jcoop1219/BME590L/Software/Software Flowchart.pdf

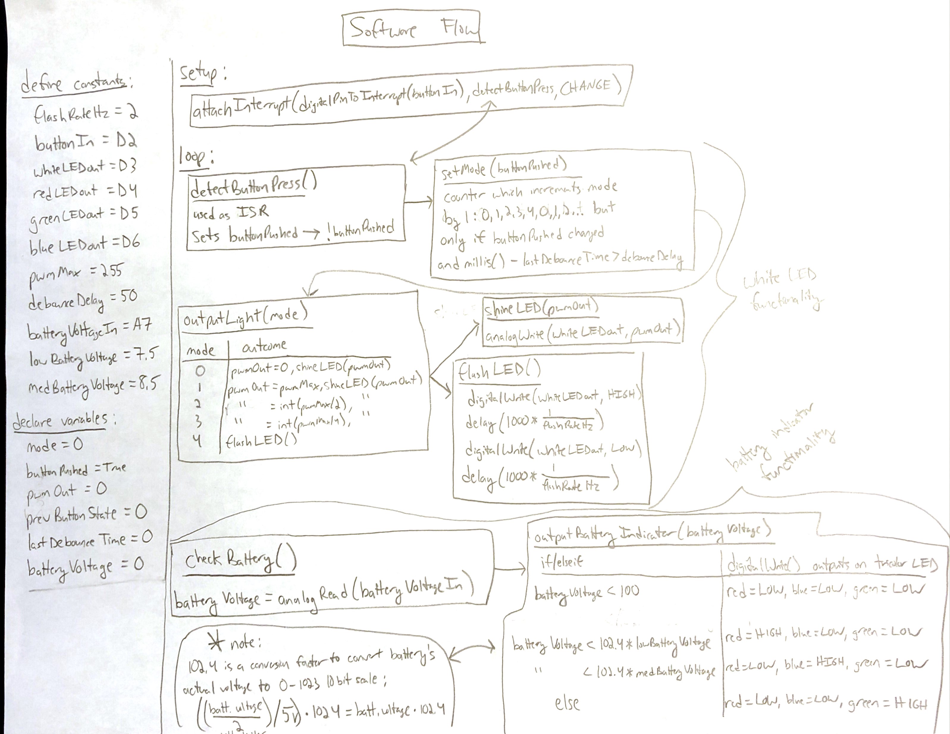
[picture p6: page 1]
